RASTRO-CR/Rastro/software/firmware/Modulo_Corredor/assets/image/GPS_EN.jpg

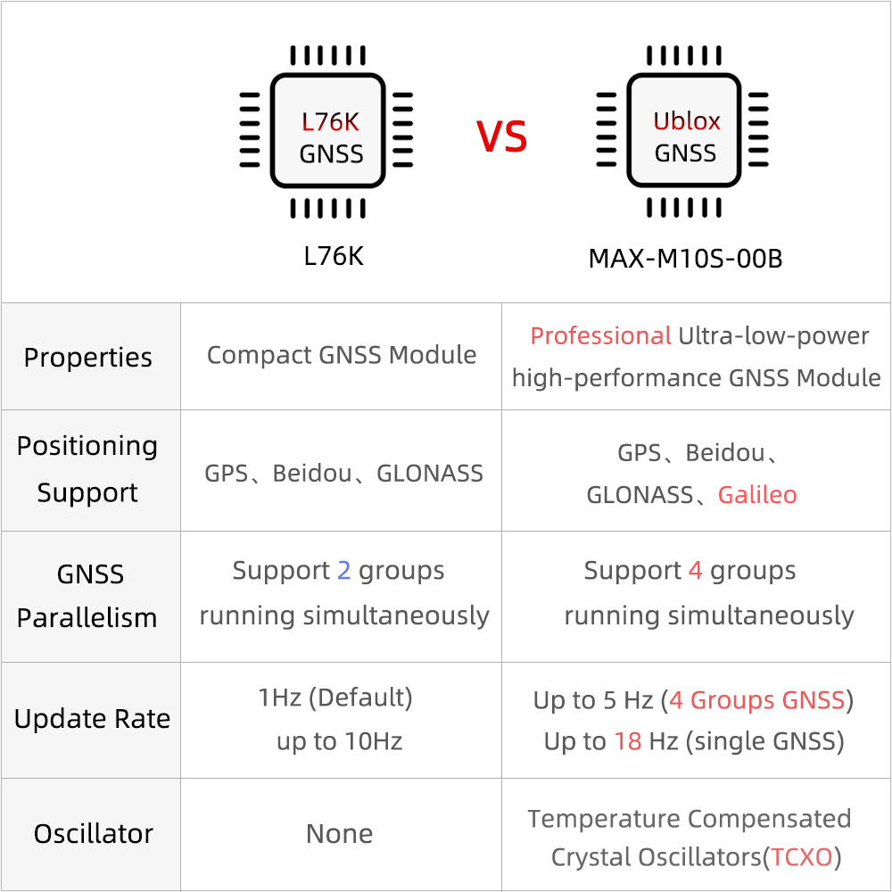
software/firmware/Modulo_Corredor/assets/image/GPS_EN.jpg
