RASTRO-CR/Rastro/software/firmware/Modulo_Corredor/assets/image/lora32_v1.8_pinmap.jpg

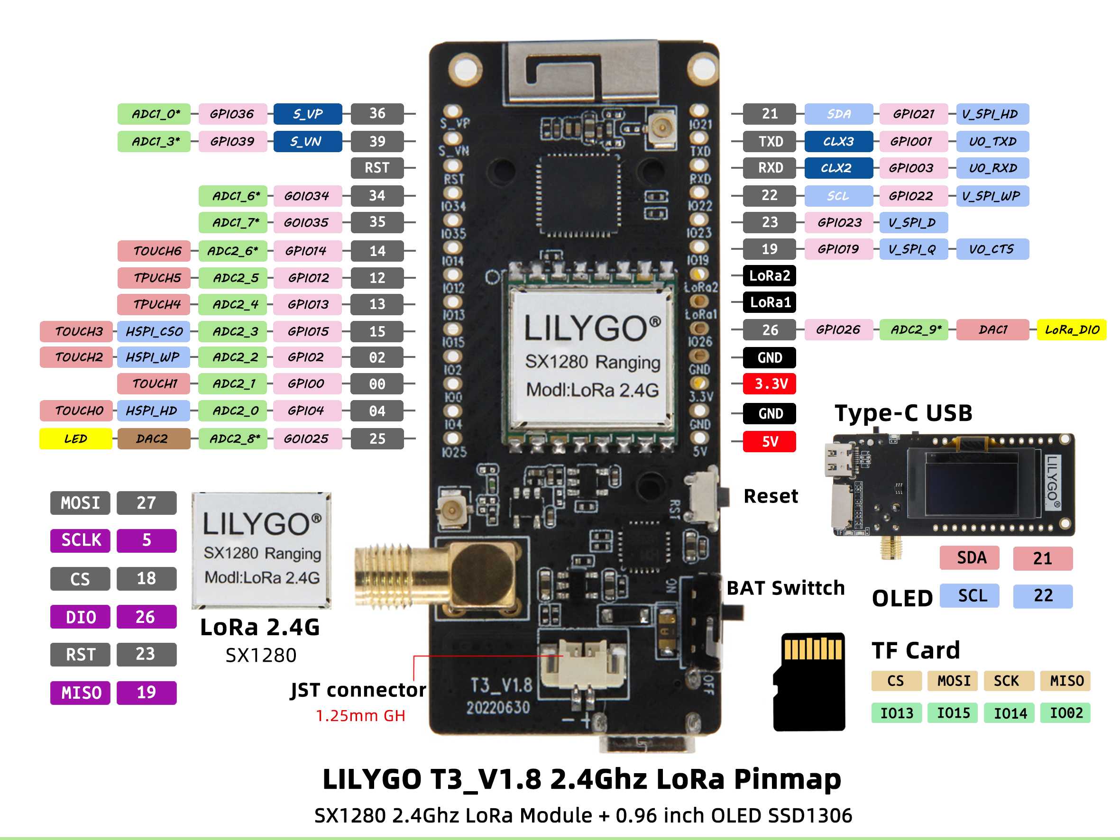
software/firmware/Modulo_Corredor/assets/image/lora32_v1.8_pinmap.jpg
