RASTRO-CR/Rastro/software/firmware/Modulo_Corredor/assets/image/lora32_v2.0_pinmap.jpg

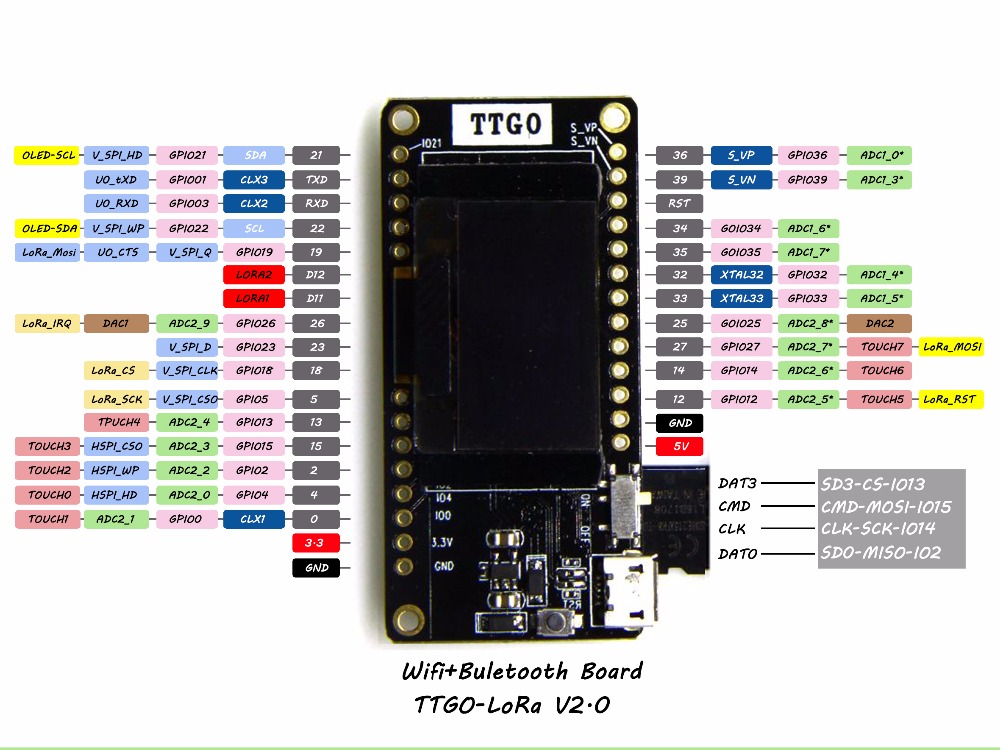
software/firmware/Modulo_Corredor/assets/image/lora32_v2.0_pinmap.jpg
