RASTRO-CR/Rastro/software/firmware/Modulo_Corredor/assets/image/T-BEAM-S3-Supreme.jpg

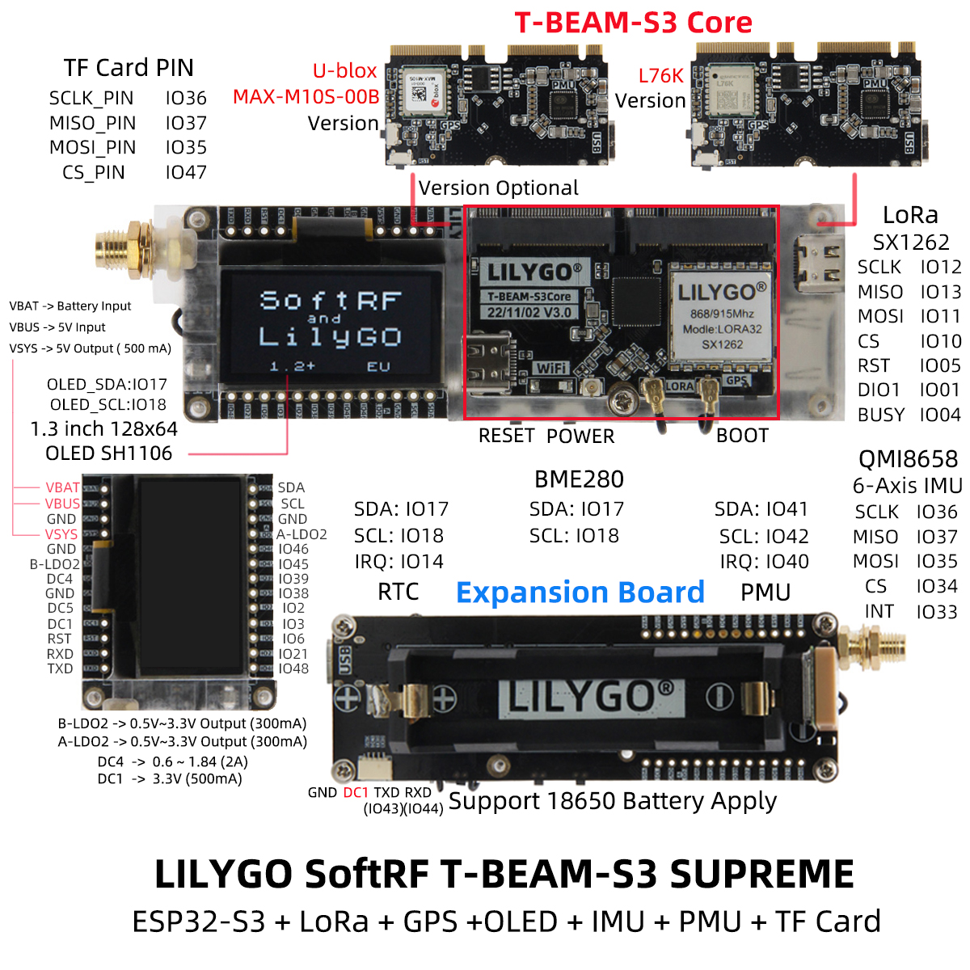
software/firmware/Modulo_Corredor/assets/image/T-BEAM-S3-Supreme.jpg
