RASTRO-CR/Rastro/software/firmware/Modulo_Corredor/assets/image/T-BEAM-S3Core.jpg

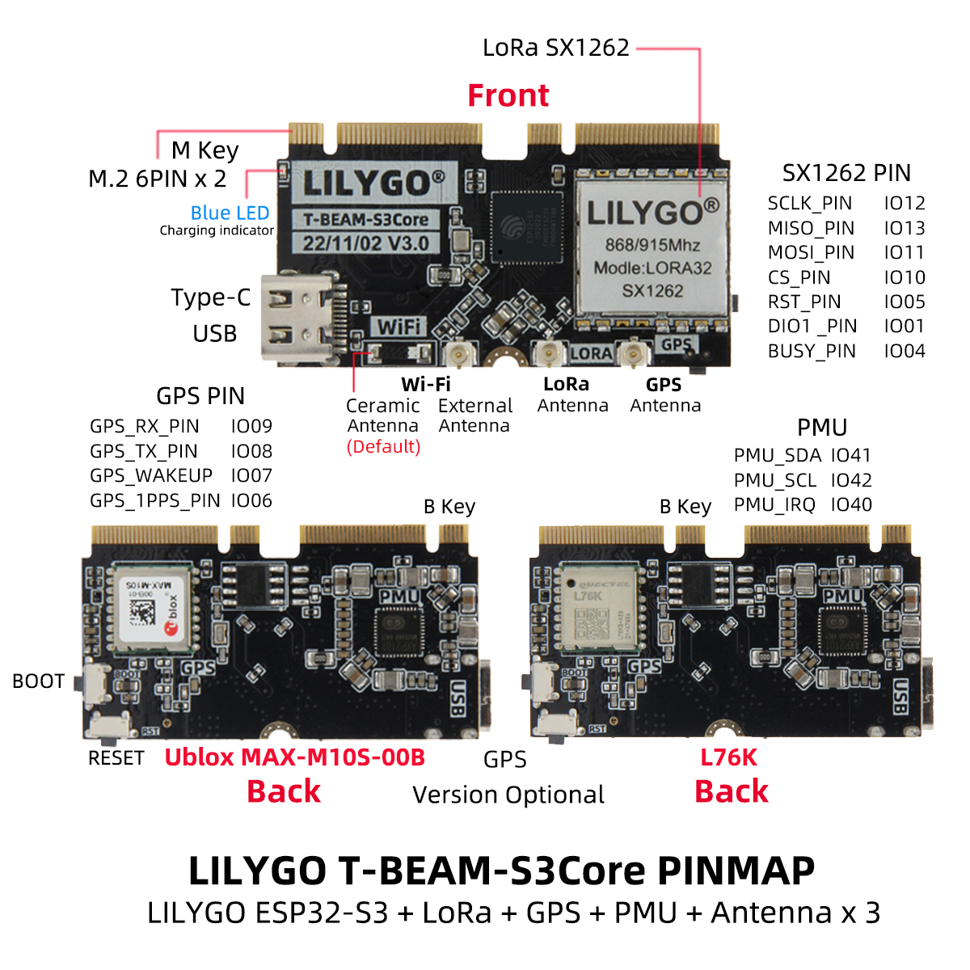
software/firmware/Modulo_Corredor/assets/image/T-BEAM-S3Core.jpg
