RASTRO-CR/Rastro/software/firmware/Modulo_Corredor/assets/image/t-beam_v1.1_pinmap.jpg

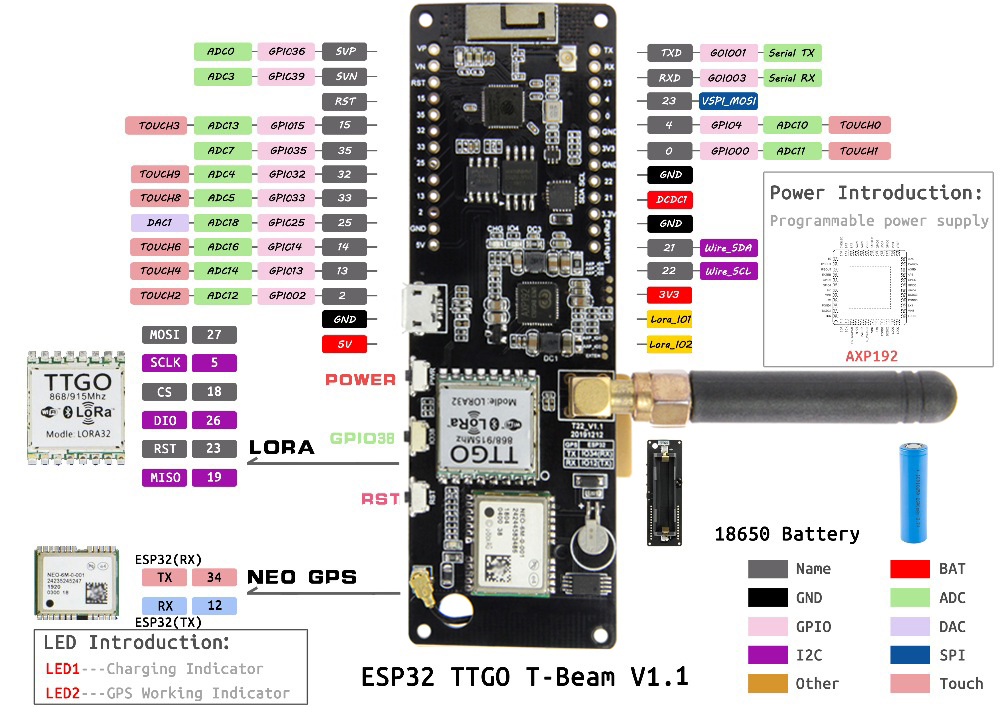
software/firmware/Modulo_Corredor/assets/image/t-beam_v1.1_pinmap.jpg
