RASTRO-CR/Rastro/software/firmware/Modulo_Corredor/dimensions/images/T3-V1.6-DXF.png

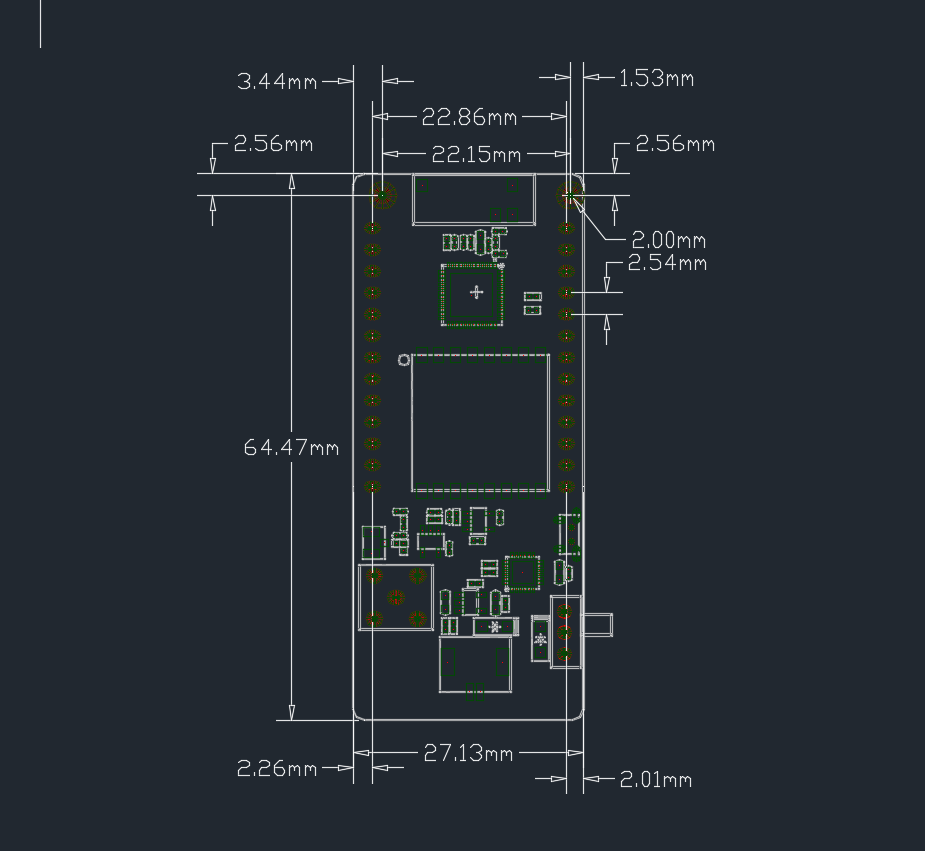
software/firmware/Modulo_Corredor/dimensions/images/T3-V1.6-DXF.png
