RASTRO-CR/Rastro/software/firmware/Modulo_Corredor/dimensions/images/T3-V1.6-PCB.jpg

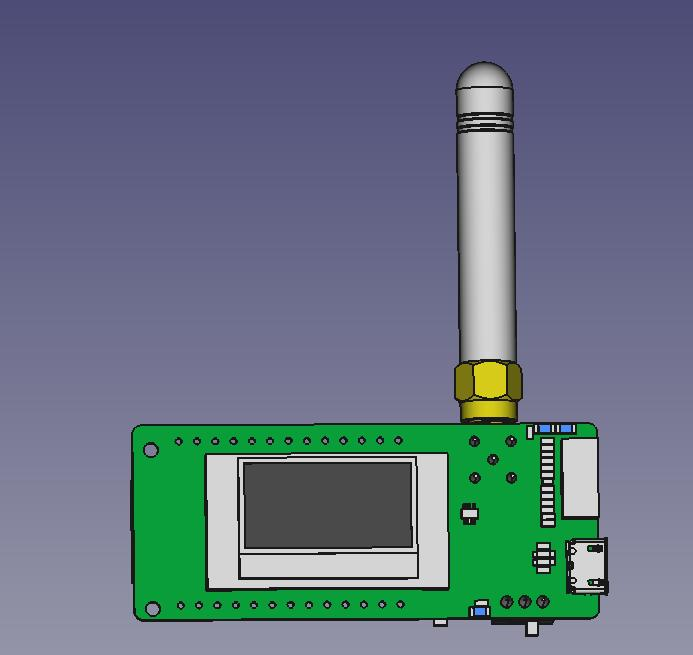
software/firmware/Modulo_Corredor/dimensions/images/T3-V1.6-PCB.jpg
