RASTRO-CR/Rastro/software/firmware/Modulo_Corredor/dimensions/images/T-Beam-Supreme-Shell.png

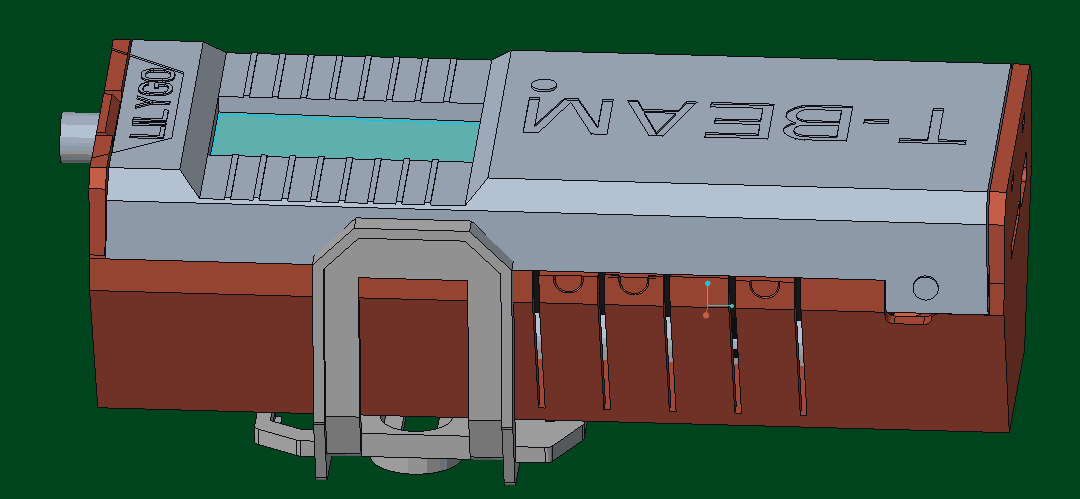
software/firmware/Modulo_Corredor/dimensions/images/T-Beam-Supreme-Shell.png
