RASTRO-CR/Rastro/software/firmware/Modulo_Corredor/docs/en/t3_s3_lr1121/images/LR1121.png

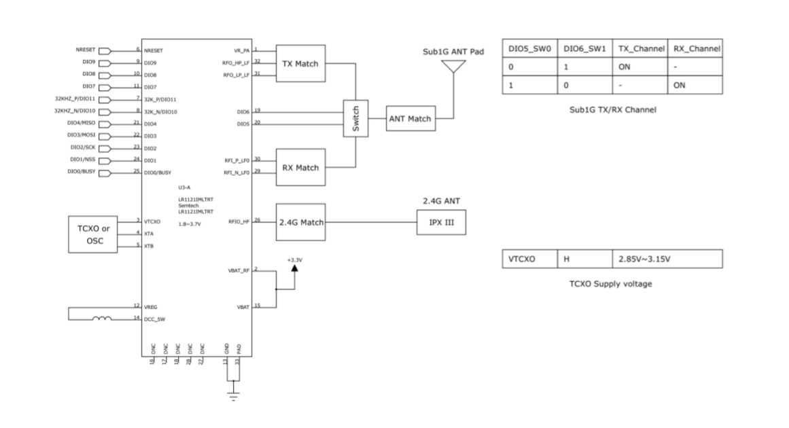
software/firmware/Modulo_Corredor/docs/en/t3_s3_lr1121/images/LR1121.png
