RASTRO-CR/Rastro/software/firmware/Modulo_Corredor/docs/en/t3_s3_lr1121/images/T3-S3-QWIIC.png

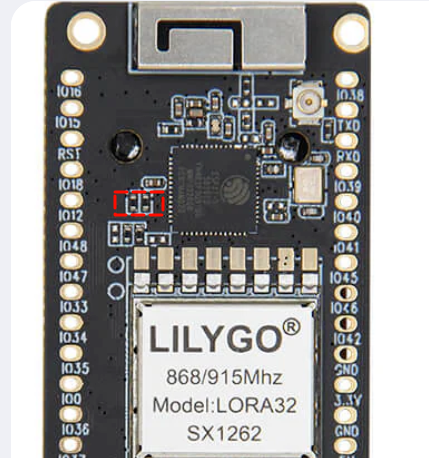
software/firmware/Modulo_Corredor/docs/en/t3_s3_lr1121/images/T3-S3-QWIIC.png
