RASTRO-CR/Rastro/software/firmware/Modulo_Corredor/docs/en/t_beam/images/HPD16E.jpg

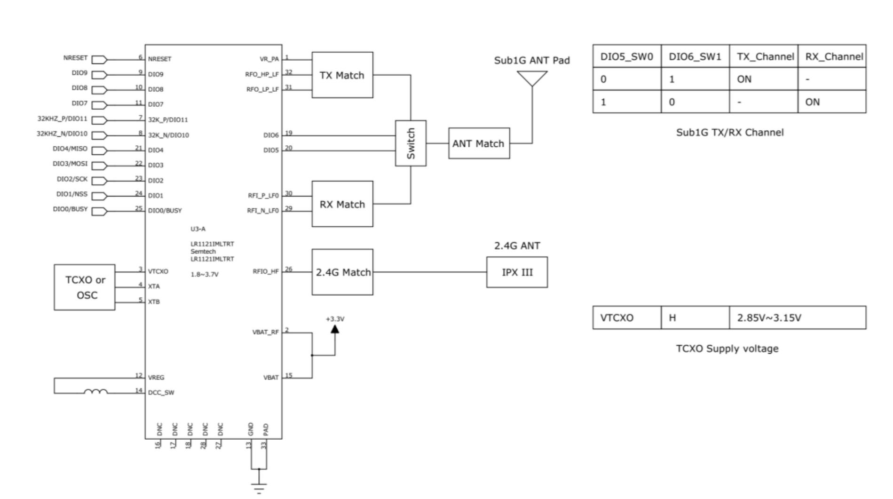
software/firmware/Modulo_Corredor/docs/en/t_beam/images/HPD16E.jpg
