RASTRO-CR/Rastro/software/firmware/Modulo_Corredor/docs/en/t_beam/images/LORA_89.jpg

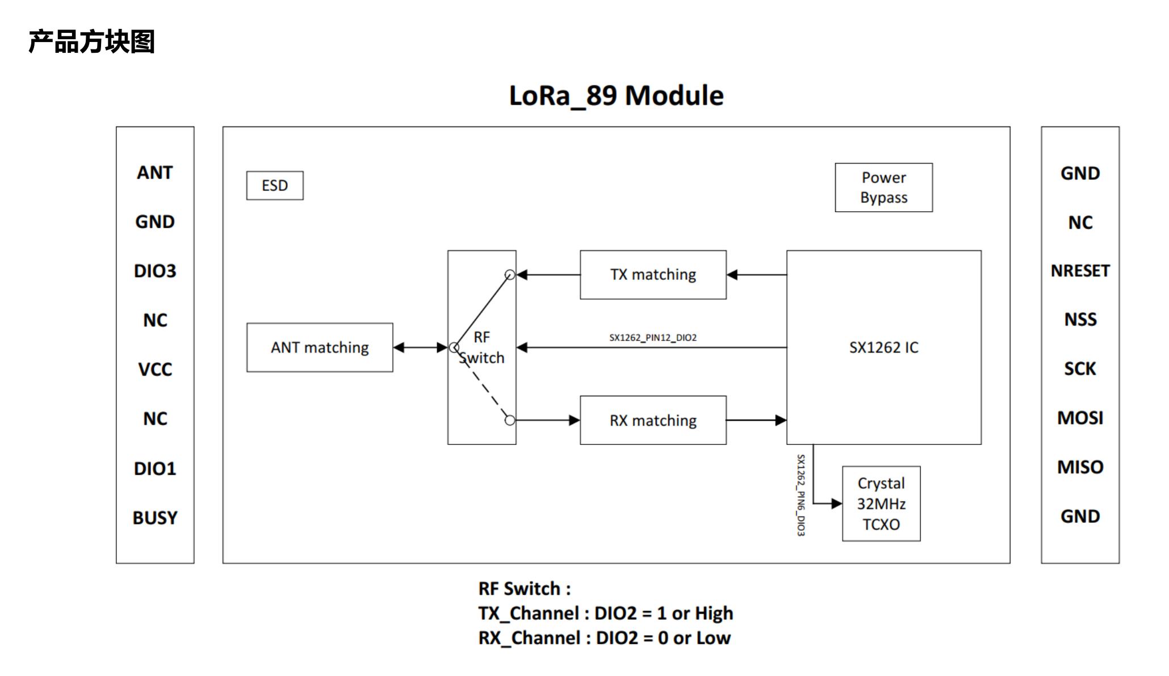
software/firmware/Modulo_Corredor/docs/en/t_beam/images/LORA_89.jpg
