RASTRO-CR/Rastro/software/firmware/Modulo_Corredor/docs/en/t_beam_2w/images/currnetA.jpg

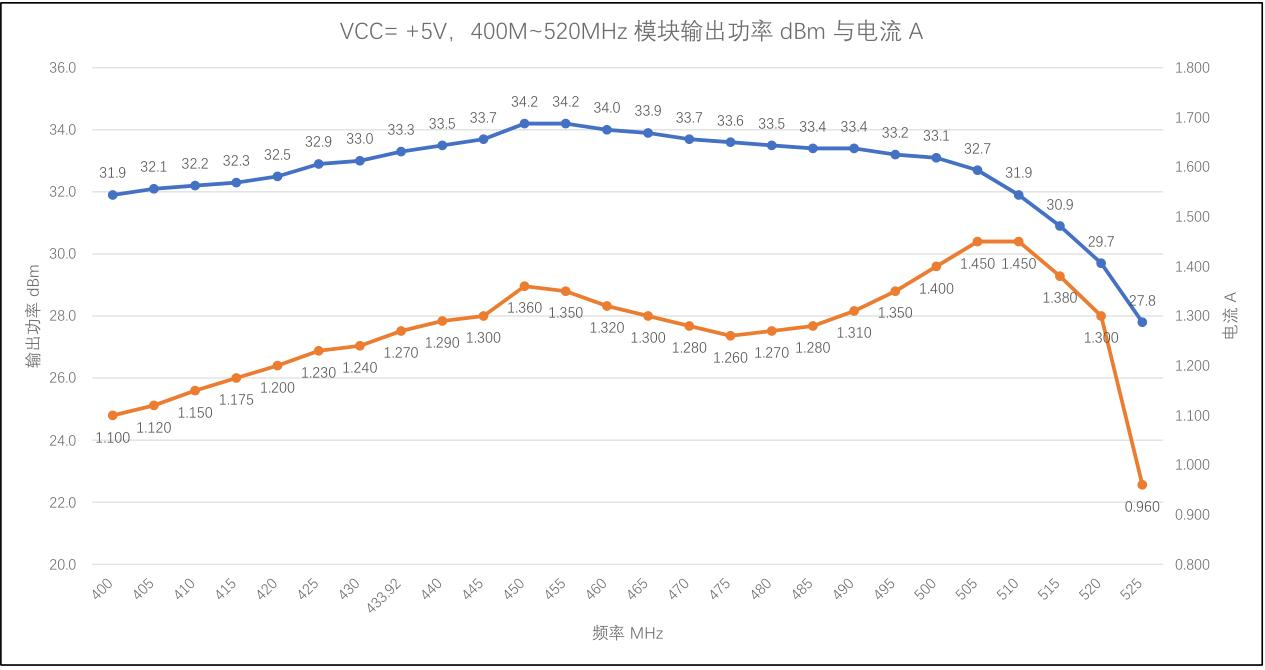
software/firmware/Modulo_Corredor/docs/en/t_beam_2w/images/currnetA.jpg
