RASTRO-CR/Rastro/software/firmware/Modulo_Corredor/docs/en/t_beam_2w/images/currnetB.jpg

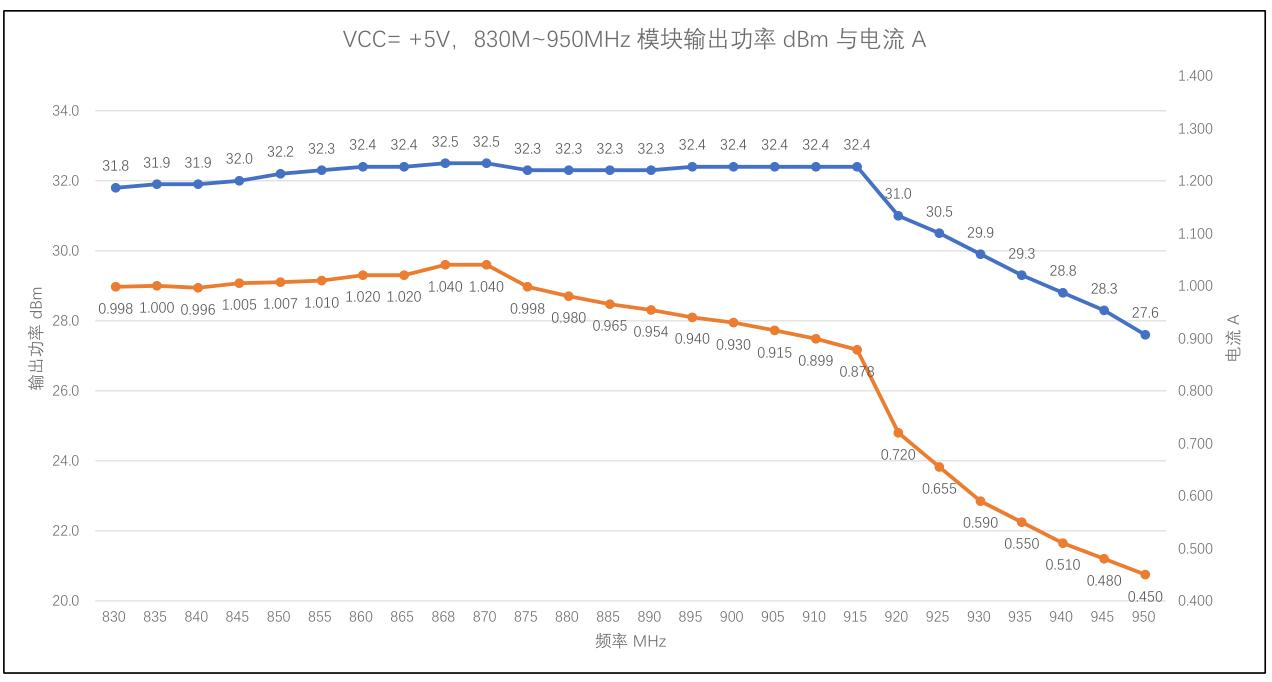
software/firmware/Modulo_Corredor/docs/en/t_beam_2w/images/currnetB.jpg
