RASTRO-CR/Rastro/software/firmware/Modulo_Corredor/docs/en/t_beam_2w/images/XY16P35.jpg

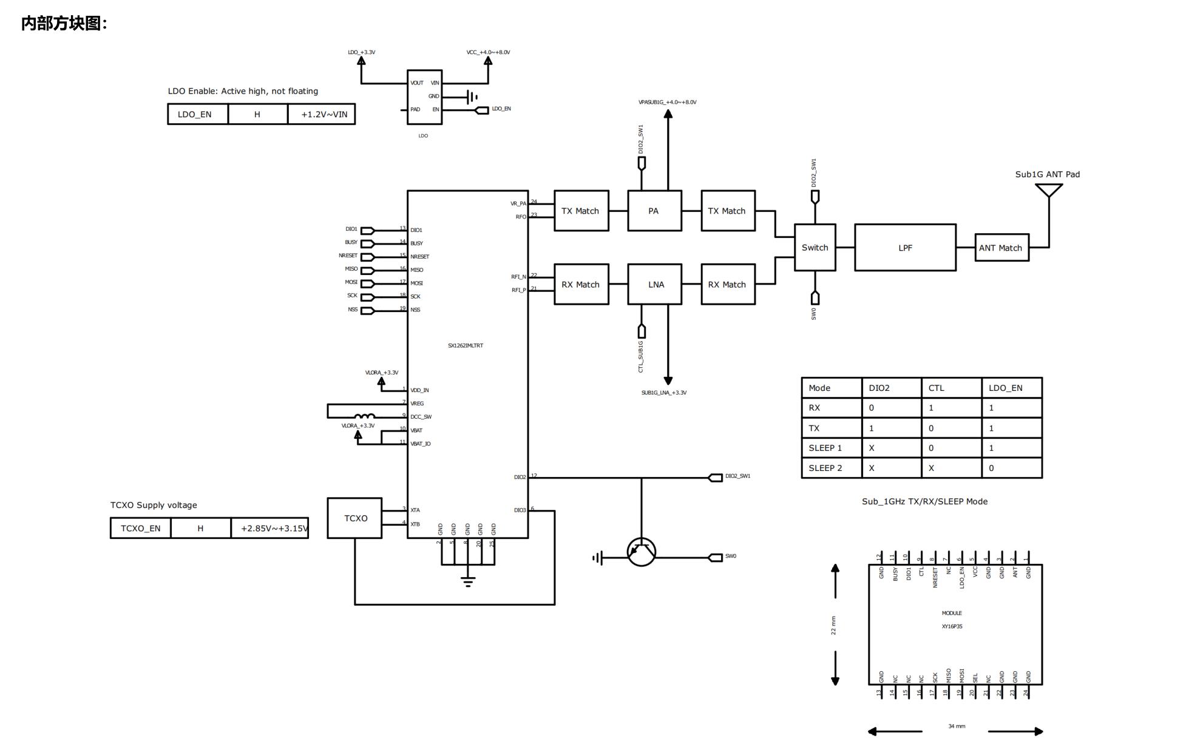
software/firmware/Modulo_Corredor/docs/en/t_beam_2w/images/XY16P35.jpg
