RASTRO-CR/Rastro/software/firmware/Modulo_Corredor/docs/en/t_beam_bpf/images/BPF.jpg

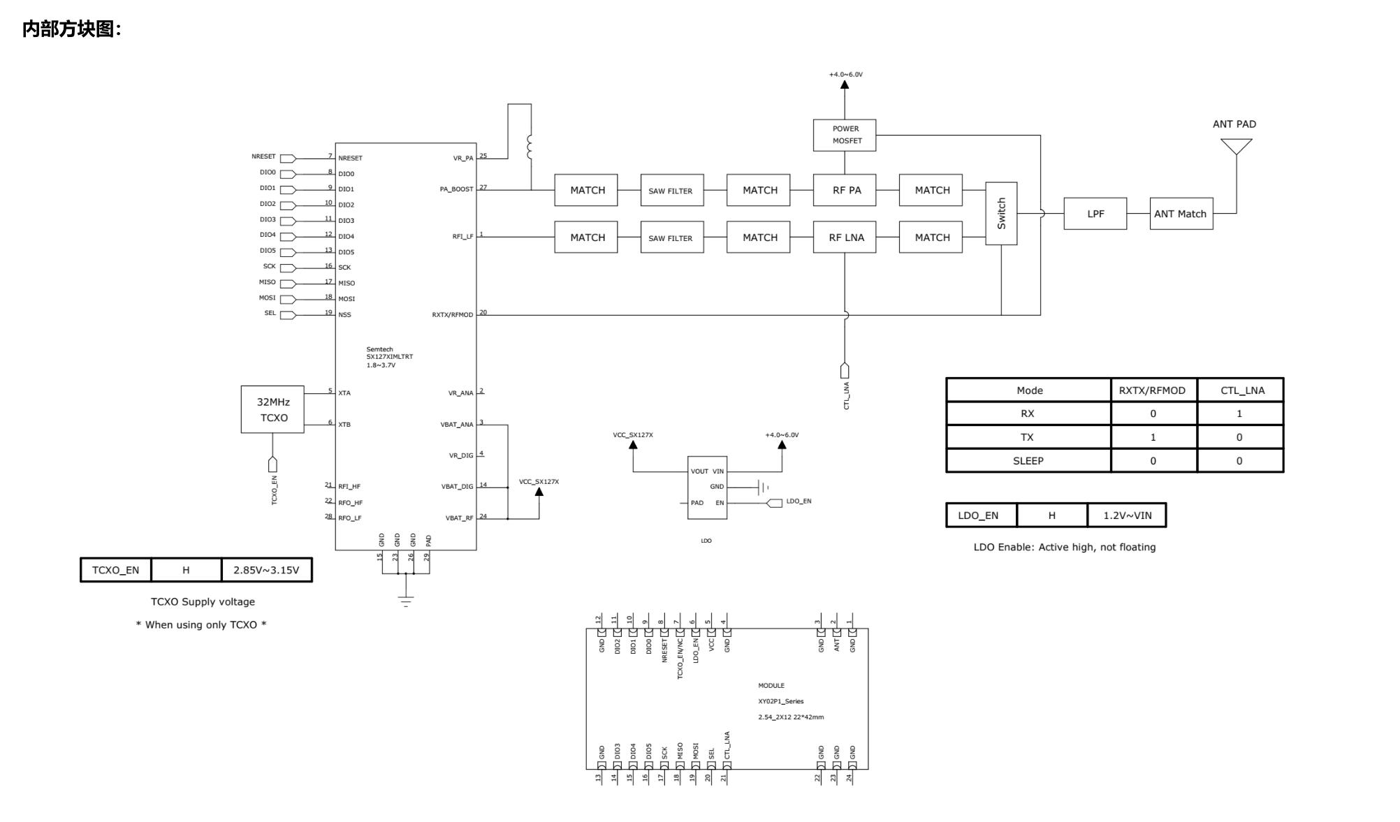
software/firmware/Modulo_Corredor/docs/en/t_beam_bpf/images/BPF.jpg
