RASTRO-CR/Rastro/software/firmware/Modulo_Corredor/examples/T3S3Factory/images/T3_S3_V1.3_DeepSleepCurrent.jpg

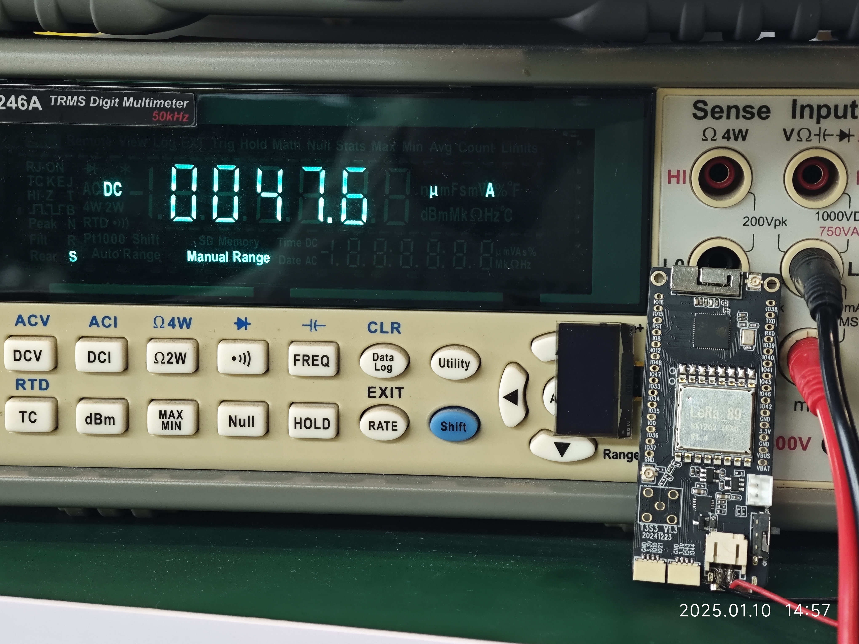
software/firmware/Modulo_Corredor/examples/T3S3Factory/images/T3_S3_V1.3_DeepSleepCurrent.jpg
