RASTRO-CR/Rastro/software/firmware/Modulo_Corredor/examples/TBeamFactory/images/TIMER_WAKEUP_ADD_GPIO_WAKEUP_SLEEP_CUR.jpg

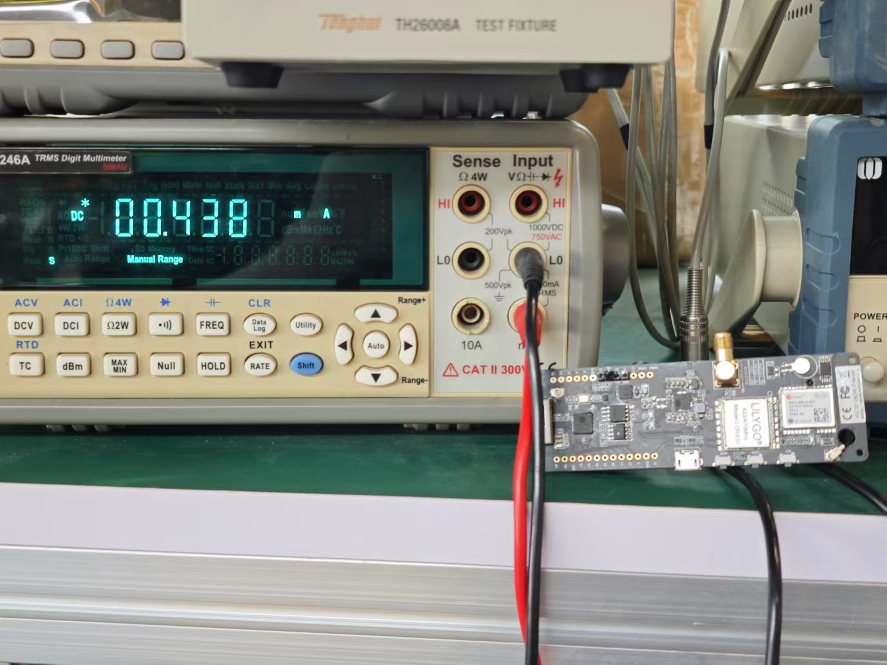
software/firmware/Modulo_Corredor/examples/TBeamFactory/images/TIMER_WAKEUP_ADD_GPIO_WAKEUP_SLEEP_CUR.jpg
