RASTRO-CR/Rastro/software/firmware/Modulo_Corredor/firmware/images/u-center2.gif

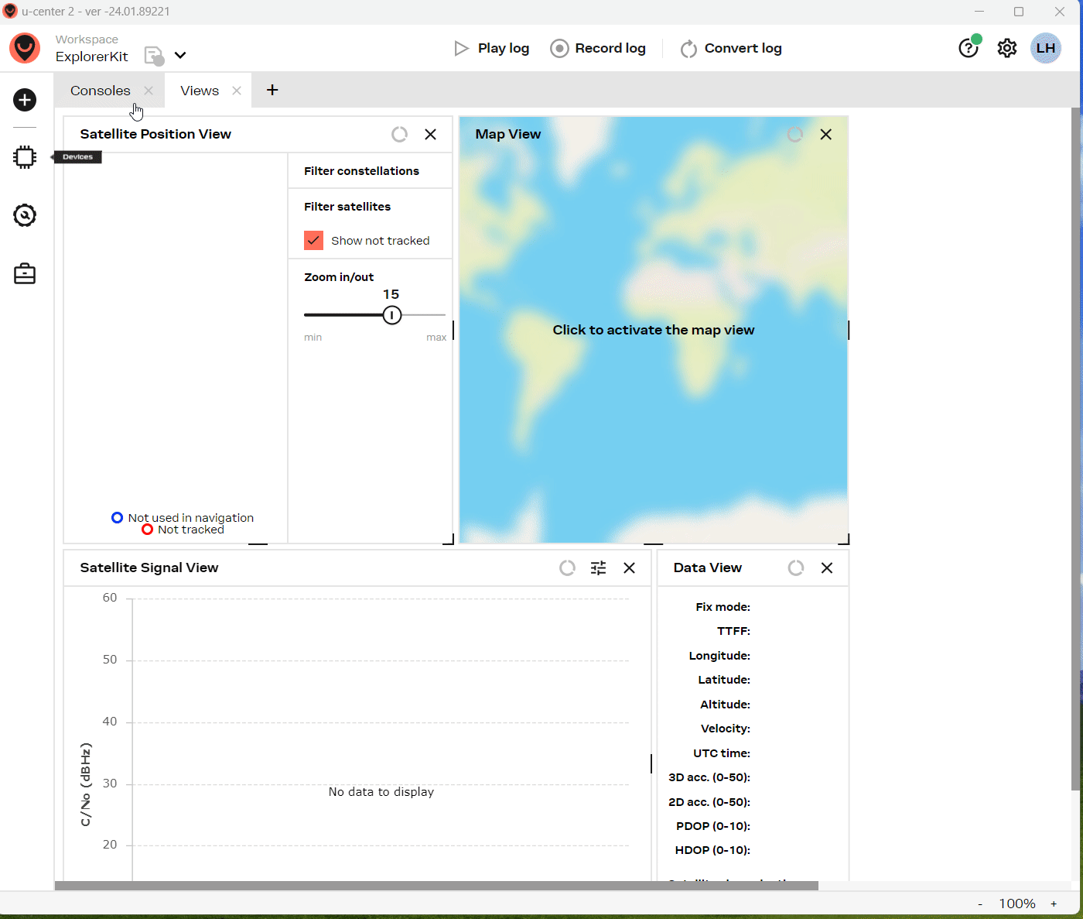
software/firmware/Modulo_Corredor/firmware/images/u-center2.gif
