RASTRO-CR/Rastro/software/firmware/Modulo_Corredor/firmware/images/web_flasher.gif

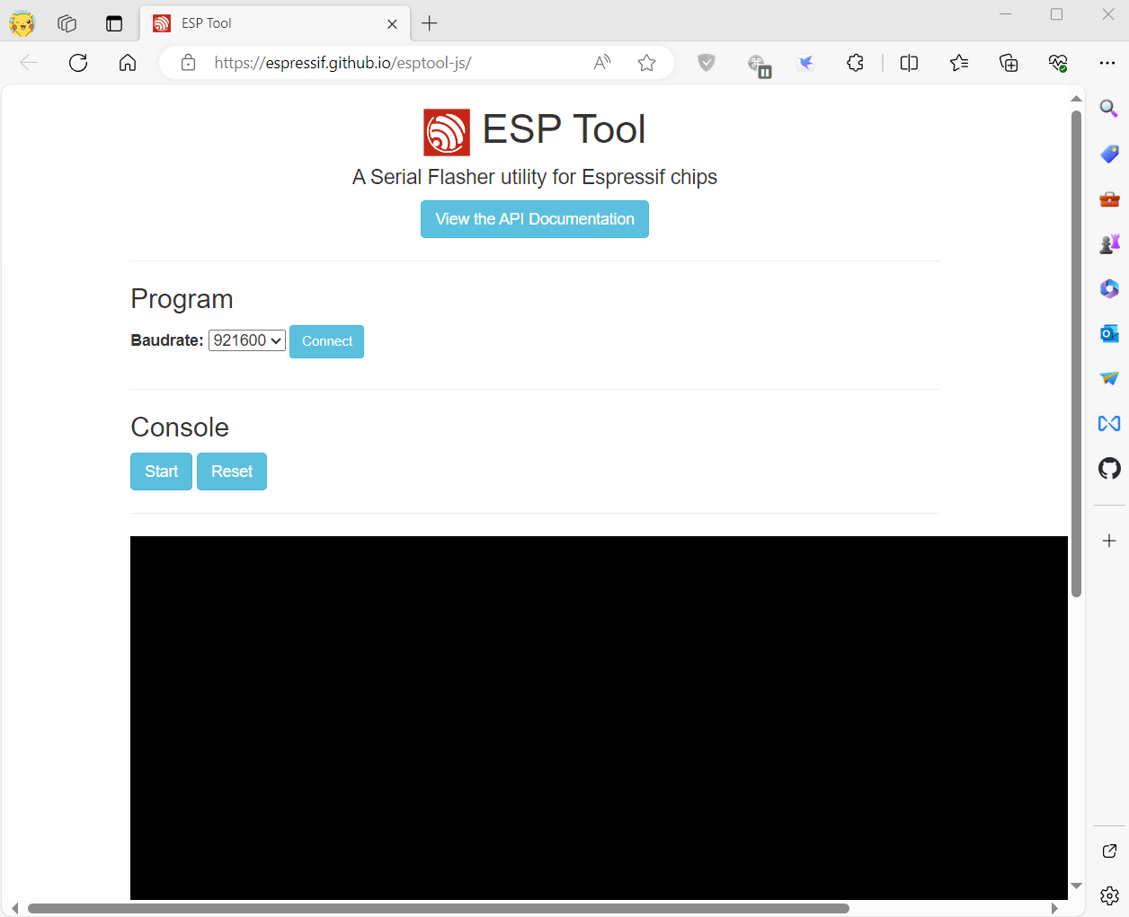
software/firmware/Modulo_Corredor/firmware/images/web_flasher.gif
