RASTRO-CR/Rastro/software/firmware/Modulo_Corredor/images/t-beams3-supreme-ant-868M.jpg

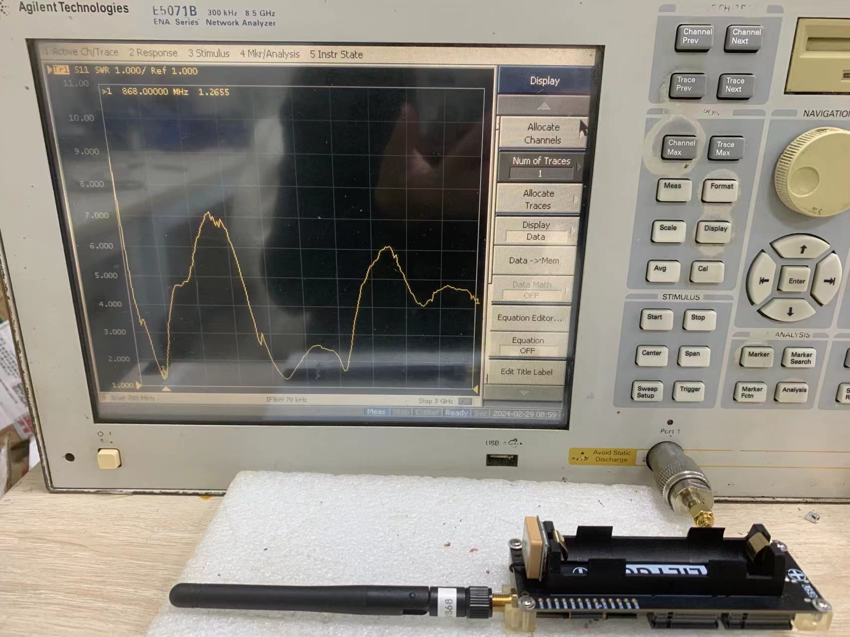
software/firmware/Modulo_Corredor/images/t-beams3-supreme-ant-868M.jpg
