RASTRO-CR/Rastro/software/firmware/Modulo_Corredor/images/t-beams3-supreme-ant-915M.jpg

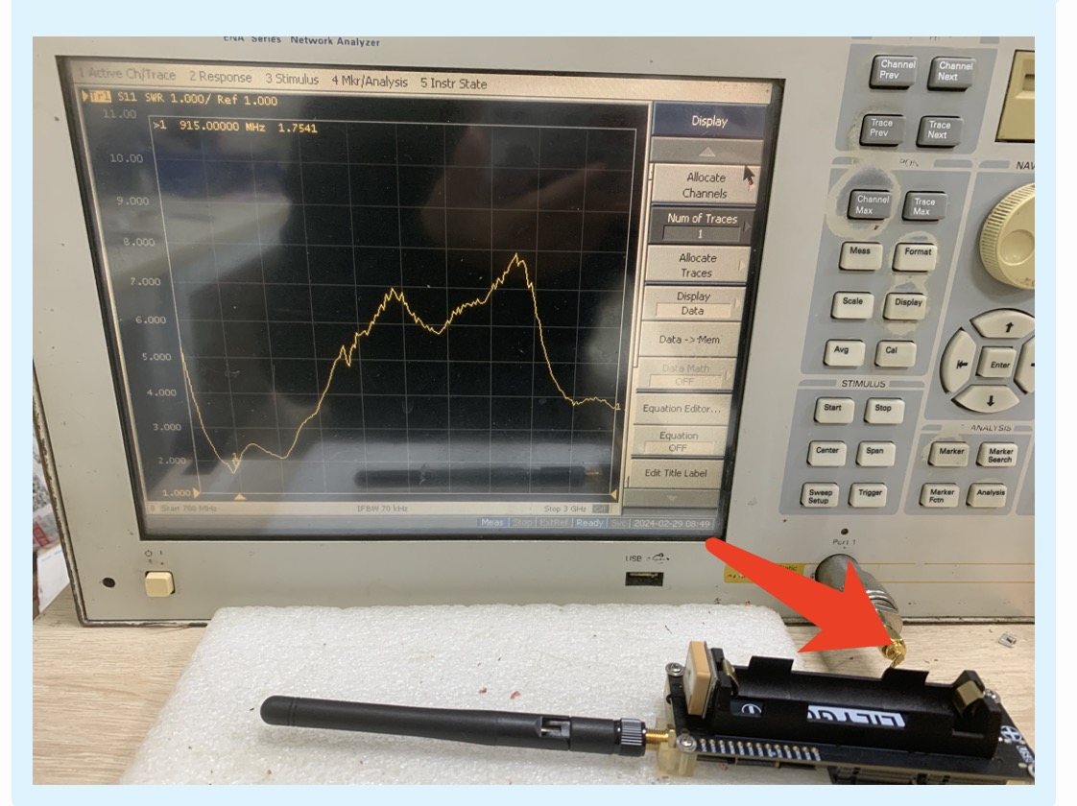
software/firmware/Modulo_Corredor/images/t-beams3-supreme-ant-915M.jpg
