RASTRO-CR/Rastro/software/firmware/Modulo_Corredor/firmware/hardware_test/lorac6_V1.0_850/SETTING.jpg

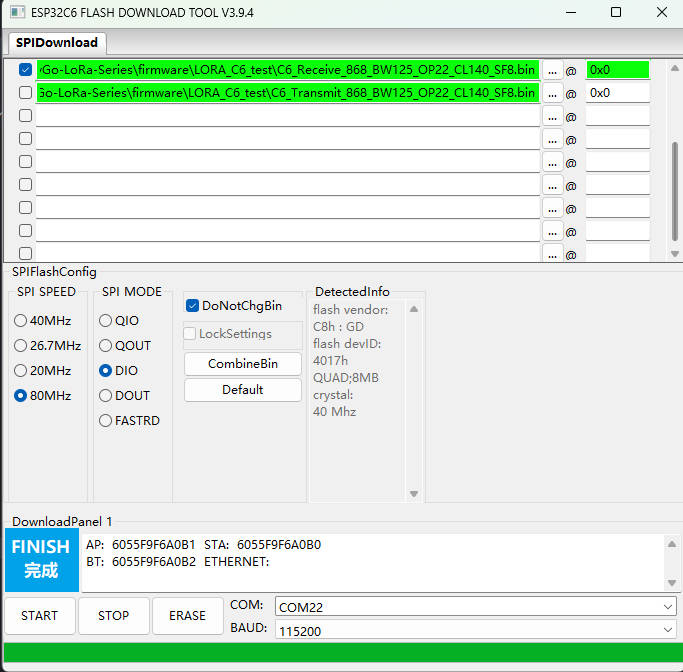
software/firmware/Modulo_Corredor/firmware/hardware_test/lorac6_V1.0_850/SETTING.jpg
