RASTRO-CR/Rastro/software/firmware/Modulo_Corredor/schematic/T3-C6_V1.0.pdf

D

6 | 5 | 4 | 3 | 2 | 1

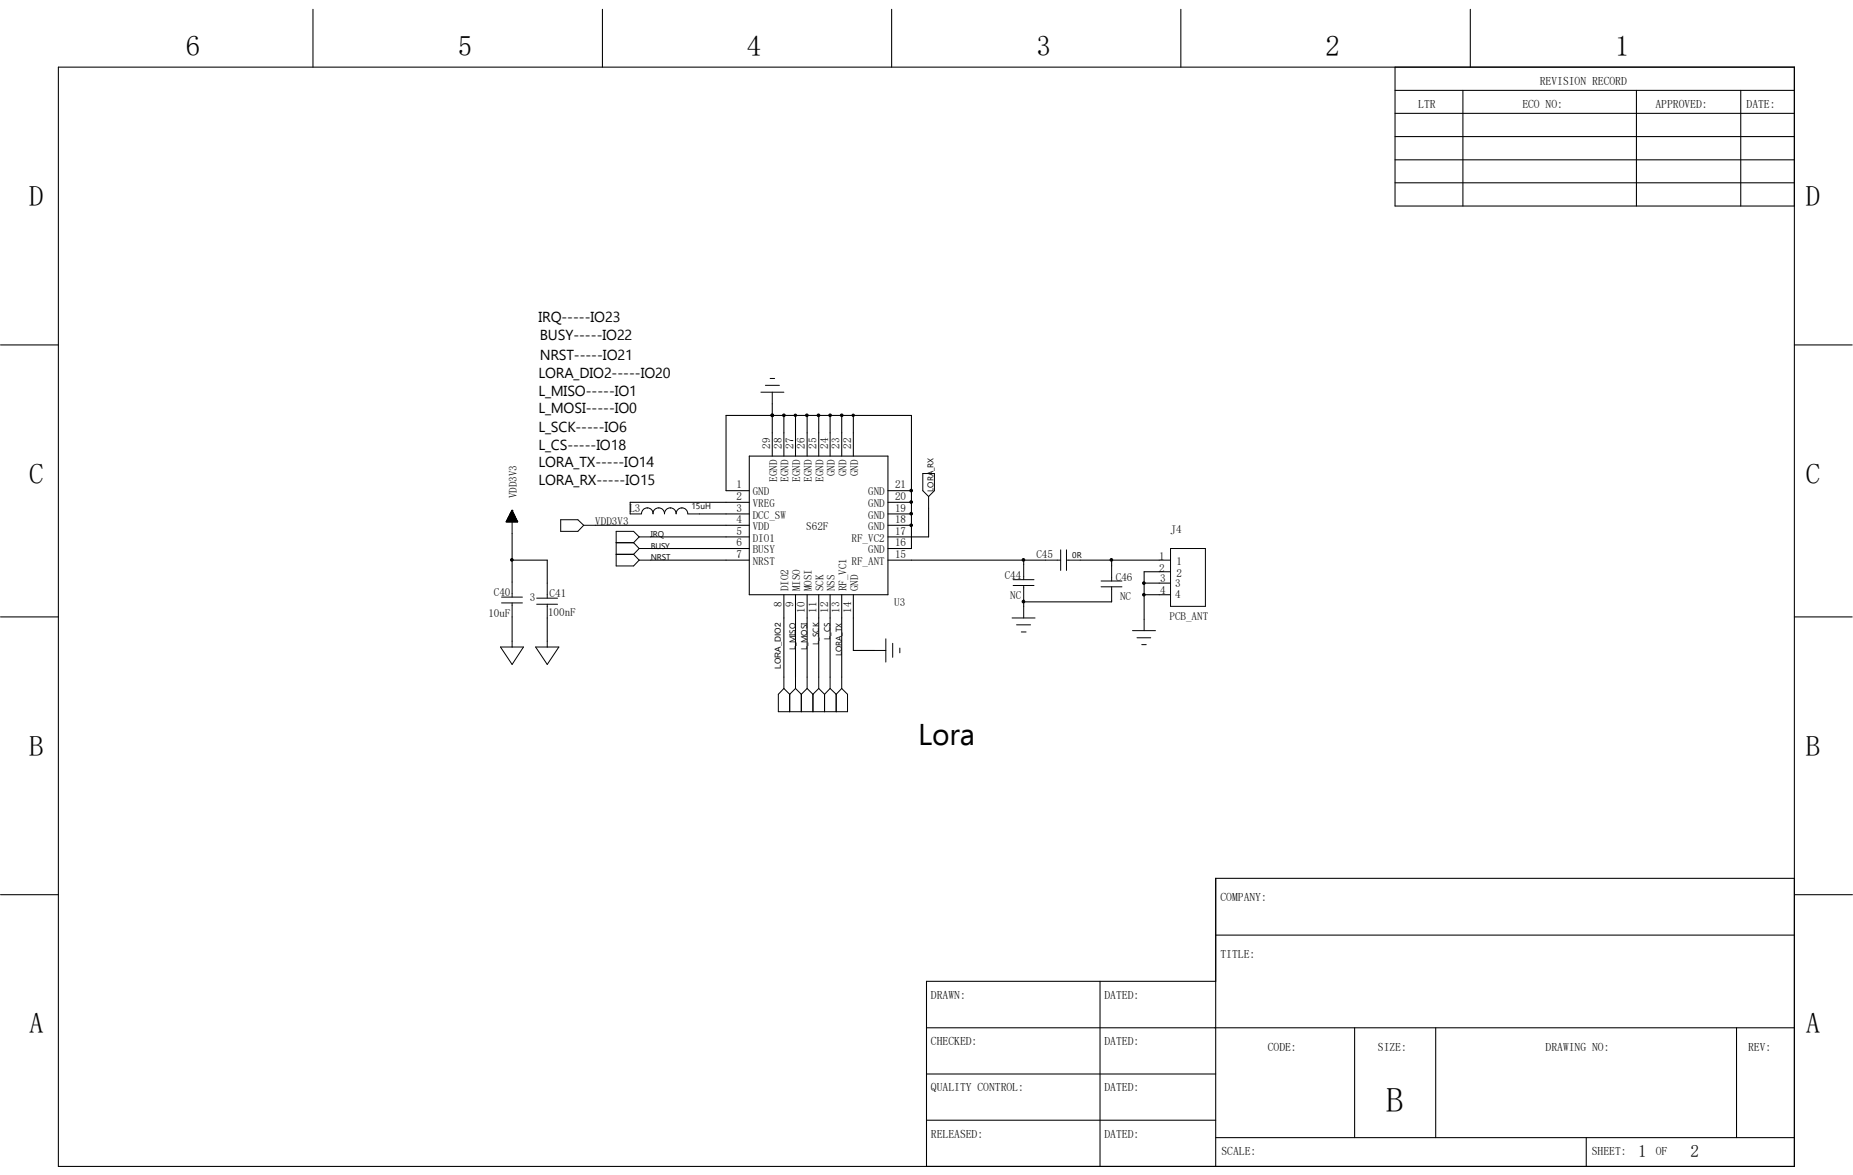
[picture p47: page 1]

REVISION RECORD

LTR | ECO NO: | APPROVED: | DATE:

21 GND ²² GND 23 GND 24 GND 25 EGND 26 EGND 27 EGND 28 EGND 29 EGND

GND 2 VREG 3 | 20 GND
DCC_SW 4 VDD 5 DIO1 6 BUSY 7 | 19 GND

9 MISO 10 MOSI 11 SCK 12 NSS 13 RF_VC1 14 GND

DRAWN: | DATED:
CHECKED: | DATED: | CODE: | SIZE: B | DRAWING NO: | REV:

QUALITY CONTROL: | DATED:

RELEASED: | DATED:

SCALE: | 1 2 SHEET: OF

D

6 | 5 | 4 | 3 | 2 | 1

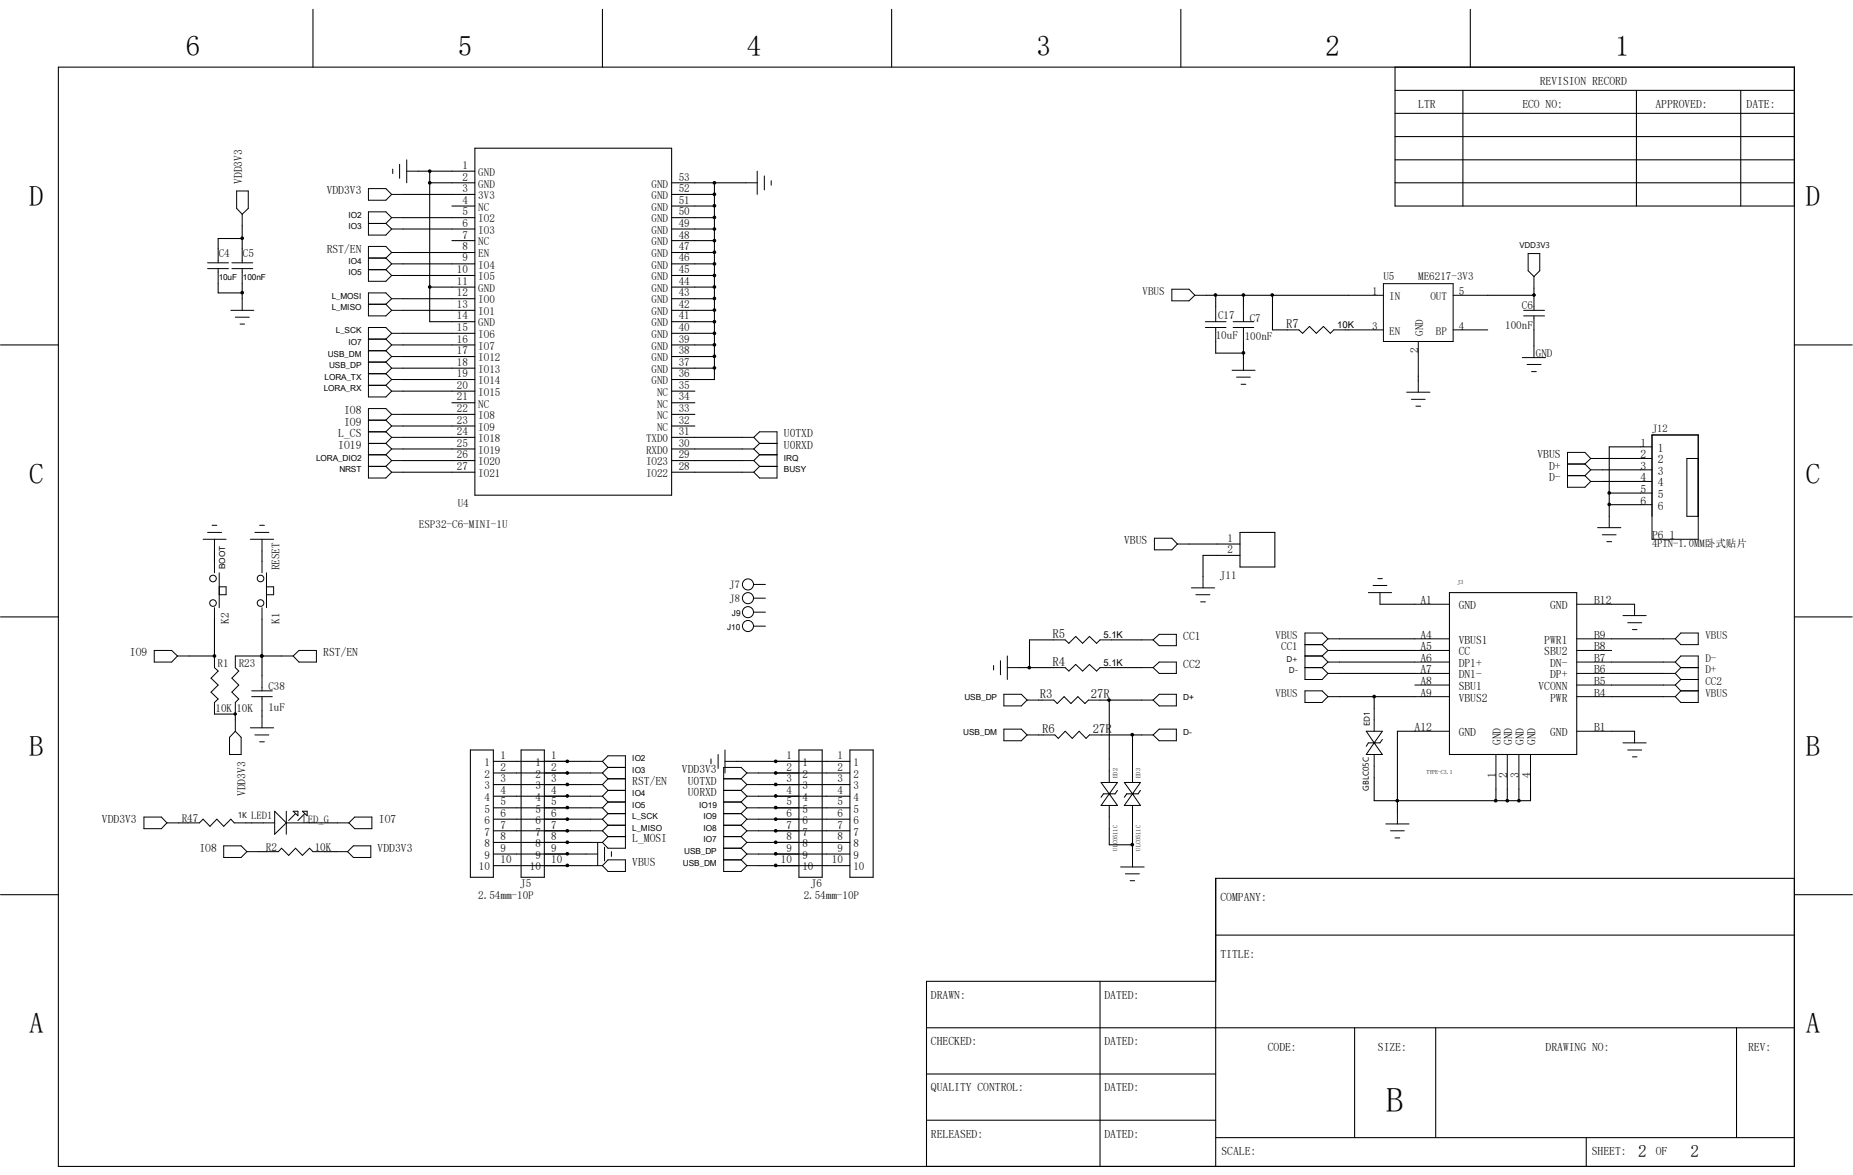
[picture p48: page 2]

REVISION RECORD

LTR | ECO NO: | APPROVED: | DATE:

GND 2 GND 3
3V3 4 NC 5 IO2 6 IO3 7 NC 8 EN 9 | 52 GND

10 10 | | 10 10

DRAWN: | DATED:
CHECKED: | DATED: | CODE: | SIZE: B | DRAWING NO: | REV:

QUALITY CONTROL: | DATED:

RELEASED: | DATED:

SCALE: | 2 2 SHEET: OF
